sinedied/esp-led-timer/src/html.h

#ifndef __HTML_H
#define __HTML_H

#include <arduino.h>

const uint32_t INDEX_HTML_SIZE = 2704;
const uint8_t INDEX_HTML[] PROGMEM = {
  31, 139, 8, 0, 0, 0, 0, 0, 0, 19, 165, 90, 107, 111, 219, 56, 
  22, 253, 158, 95, 113, 71, 45, 42, 123, 234, 103, 50, 45, 6, 182, 229, 
  5, 250, 194, 20, 216, 118, 138, 73, 7, 251, 161, 40, 18, 90, 186, 182, 
  185, 145, 72, 173, 72, 197, 241, 6, 249, 239, 11, 146, 162, 68, 201, 15, 
  217, 89, 32, 128, 77, 242, 242, 240, 240, 94, 222, 7, 233, 204, 126, 137, 
  120, 40, 183, 41, 194, 90, 38, 241, 252, 98, 166, 62, 32, 38, 108, 21, 
  120, 200, 60, 213, 129, 36, 154, 95, 0, 204, 18, 148, 4, 194, 53, 201, 
  4, 202, 192, 203, 229, 178, 255, 187, 7, 195, 106, 136, 145, 4, 3, 239, 
  158, 226, 38, 229, 153, 244, 32, 228, 76, 34, 147, 129, 183, 161, 145, 92, 
  7, 17, 222, 211, 16, 251, 186, 209, 3, 202, 168, 164, 36, 238, 139, 144, 
  196, 24, 140, 7, 35, 11, 37, 169, 140, 113, 254, 157, 38, 152, 193, 123, 
  206, 100, 198, 227, 217, 208, 116, 94, 204, 134, 134, 204, 76, 200, 173, 106, 
  3, 44, 120, 180, 133, 199, 11, 0, 128, 37, 103, 178, 191, 36, 9, 141, 
  183, 19, 240, 175, 113, 197, 17, 254, 254, 236, 247, 160, 79, 210, 52, 198, 
  190, 216, 10, 137, 73, 15, 222, 197, 148, 221, 125, 33, 225, 181, 110, 127, 
  226, 76, 246, 224, 47, 190, 224, 146, 247, 192, 255, 3, 227, 123, 148, 52, 
  36, 240, 21, 115, 244, 123, 32, 8, 19, 125, 129, 25, 93, 78, 245, 42, 
  33, 143, 121, 54, 129, 23, 227, 241, 216, 116, 36, 228, 193, 236, 105, 2, 
  111, 71, 163, 244, 193, 246, 102, 43, 202, 38, 48, 2, 146, 75, 174, 250, 
  158, 46, 0, 150, 20, 227, 72, 160, 44, 24, 43, 5, 17, 202, 48, 235, 
  43, 3, 76, 128, 178, 152, 50, 236, 11, 250, 95, 52, 40, 11, 158, 69, 
  152, 77, 96, 156, 62, 128, 224, 49, 141, 224, 197, 213, 213, 149, 59, 214, 
  207, 72, 68, 115, 49, 129, 55, 118, 229, 136, 138, 52, 38, 219, 9, 44, 
  99, 44, 186, 212, 183, 126, 68, 51, 12, 37, 229, 108, 162, 246, 144, 39, 
  172, 78, 116, 140, 137, 101, 25, 147, 5, 198, 174, 82, 55, 72, 87, 107, 
  57, 129, 5, 143, 35, 43, 180, 200, 165, 228, 76, 217, 49, 205, 101, 15, 
  4, 198, 24, 218, 125, 37, 148, 89, 149, 140, 166, 21, 140, 218, 87, 185, 
  16, 64, 74, 162, 136, 178, 213, 4, 70, 131, 55, 182, 175, 84, 91, 213, 
  245, 28, 29, 44, 72, 120, 183, 202, 120, 206, 162, 9, 188, 64, 196, 58, 
  105, 187, 181, 24, 31, 38, 112, 105, 199, 244, 70, 38, 140, 203, 206, 15, 
  101, 141, 192, 15, 215, 24, 222, 45, 248, 131, 255, 179, 219, 216, 159, 153, 
  249, 91, 29, 117, 178, 230, 247, 152, 21, 10, 177, 13, 51, 205, 180, 138, 
  201, 53, 110, 81, 212, 80, 232, 132, 132, 146, 222, 163, 133, 177, 173, 2, 
  199, 52, 247, 1, 133, 97, 216, 0, 138, 168, 32, 139, 24, 35, 11, 85, 
  181, 11, 48, 219, 81, 192, 241, 148, 132, 84, 110, 181, 238, 143, 107, 49, 
  53, 90, 162, 209, 207, 110, 49, 247, 132, 51, 151, 241, 141, 25, 32, 49, 
  93, 177, 62, 149, 152, 136, 9, 132, 200, 36, 102, 117, 219, 23, 86, 84, 
  43, 173, 199, 197, 2, 18, 31, 100, 95, 207, 172, 207, 113, 207, 213, 239, 
  225, 127, 54, 141, 83, 100, 113, 68, 158, 36, 36, 179, 129, 34, 204, 51, 
  161, 124, 56, 229, 116, 119, 245, 145, 235, 9, 235, 210, 104, 197, 33, 28, 
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
};

#endif // __HTML_H
